sbelectronics/z8000/cpm8kdisks/romdisk/sgtty.h

/* sgtty.h - tty control information */
/*	Note reduced contents for CP/M implementation... */
struct sgttyb{
	char	sg_ispeed;	/* ignored */
	char	sg_ospeed;	/* ignored */
	char	sg_erase;	/* ignored */
	char	sg_kill;	/* ignored */
	int	sg_flags;	
};
#define RAW	0000040
#define CRMOD	0000020
#define ECHO	0000010
#define LCASE	0000004
#define CBREAK	0000002
